StevenNaliwajka/TF2SentryEE/Documentation/1-TurretGuts/PCB/Turret/TurretMainBoard/TurretMainBoard.kicad_sch

## KiCad design Documentation/1-TurretGuts/PCB/Turret/TurretMainBoard/TurretMainBoard.kicad_sch (2025-07-17)

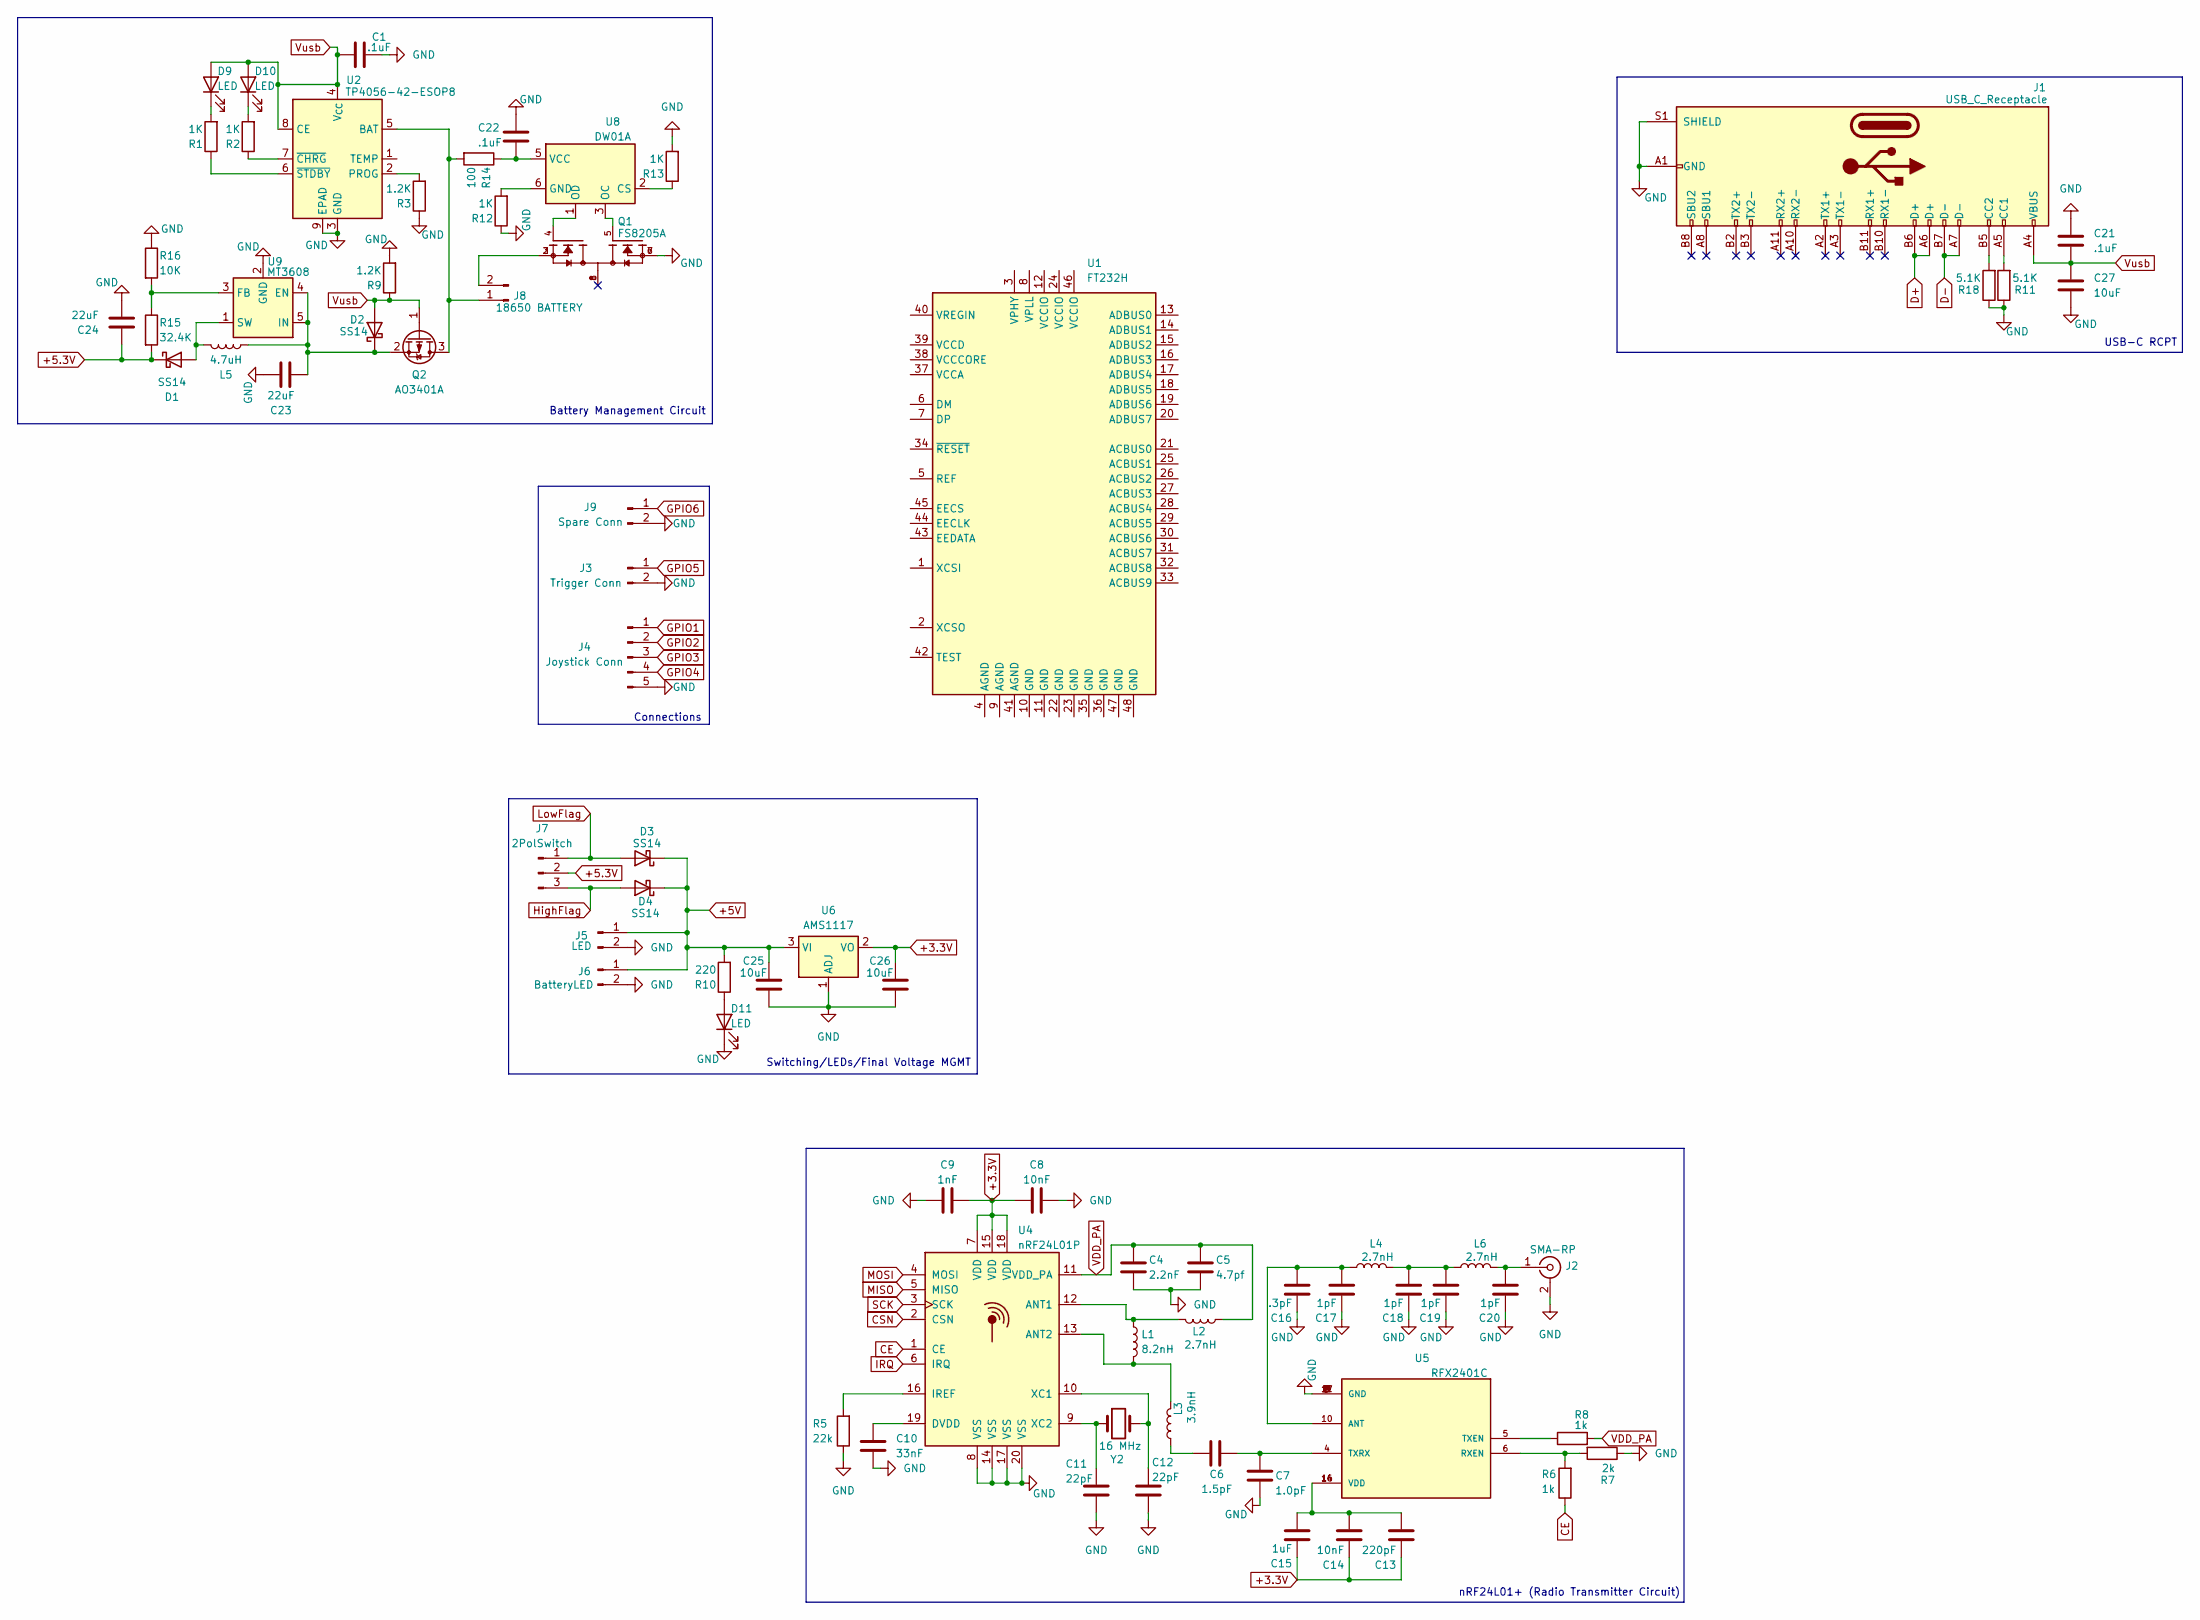
[picture p3: schematic TurretMainBoard.kicad_sch]

Parts:
C1, C21, C22: .1uF
C4: 2.2nF
C5: 4.7pf
C6: 1.5pF
C7: 1.0pF
C8, C14: 10nF
C9: 1nF
C10: 33nF
C11, C12: 22pF
C13: 220pF
C15: 1uF
C16: .3pF
C17, C18, C19, C20: 1pF
C23, C24: 22uF
C25, C26, C27: 10uF
D1, D2, D3, D4: SS14; D_SMA
D9, D10, D11: LED
J1: USB_C_Receptacle
J2: SMA-RP
J3: Trigger Conn
J4: Joystick Conn
J5: LED
J6: BatteryLED
J7: 2PolSwitch
J8: 18650 BATTERY
J9: Spare Conn
L1: 8.2nH
L2, L4, L6: 2.7nH
L3: 3.9nH
L5: 4.7uH
Q1: FS8205A; SOP65P640X120-8N; PARTREV 1.7
Q2: AO3401A; SOT-23
R1, R2, R12, R13: 1K
R3, R9: 1.2K
R5: 22k
R6, R8: 1k
R7: 2k
R10: 220
R11, R18: 5.1K
R14: 100
R15: 32.4K
R16: 10K
U1: FT232H
U2: TP4056-42-ESOP8; SOIC-8-1EP_3.9x4.9mm_P1.27mm_EP2.41x3.3mm_ThermalVias
U4: nRF24L01P; QFN-20-1EP_4x4mm_P0.5mm_EP2.5x2.5mm
U5: RFX2401C; QFN50P300X300X60-17N
U6: AMS1117; SOT-223-3_TabPin2
U8: DW01A; SOT-23-6
U9: MT3608; SOT-23-6
Y2: 16 MHz

Connections:
+3.3V: C8.1, C9.2, C13.2, C14.2, C15.2, C26.1, U4.7 (VDD), U4.15 (VDD), U4.18 (VDD), U6.2 (VO)
+5.3V: C24.2, D1.1 (K), J7.2, R15.2
+5V: C25.1, D3.1 (K), D4.1 (K), J5.1, J6.1, R10.2, U6.3 (VI)
CE: R6.1, U4.1 (CE)
CSN: U4.2 (CSN)
D+: J1.A6 (D+), J1.B6 (D+)
D-: J1.A7 (D-), J1.B7 (D-)
GND: C1.2, C4.2, C5.2, C7.1, C8.2, C9.1, C10.2, C11.2, C12.2, C16.2, C17.2, C18.2, C19.2, C20.2, C21.1, C22.1, C23.2, C24.1, C25.2, C26.2, C27.2, D11.1 (K), J1.A1 (GND), J1.A12 (GND), J1.B1 (GND), J1.B12 (GND), J1.S1 (SHIELD), J2.2 (Ext), J3.2, J4.5, J5.2, J6.2, J9.2, Q1.6, Q1.7, R3.1, R5.1, R7.1, R9.2, R11.1, R12.1, R13.2, R16.1, R18.1, U2.3 (GND), U2.9 (EPAD), U4.8 (VSS), U4.14 (VSS), U4.17 (VSS), U4.20 (VSS), U5.2 (GND), U5.3 (GND), U5.8 (GND), U5.9 (GND), U5.11 (GND), U5.17 (GND), U6.1 (ADJ), U9.2 (GND)
GPIO1: J4.1
GPIO2: J4.2
GPIO3: J4.3
GPIO4: J4.4
GPIO5: J3.1
GPIO6: J9.1
HighFlag: D4.2 (A), J7.3
IRQ: U4.6 (IRQ)
LowFlag: D3.2 (A), J7.1
MISO: U4.5 (MISO)
MOSI: U4.4 (MOSI)
unnamed: C6.1, L3.1
unnamed: C6.2, C7.2, U5.4 (TXRX)
unnamed: C10.1, U4.19 (DVDD)
unnamed: C11.1, U4.9 (XC2), Y2.1
unnamed: C12.1, U4.10 (XC1), Y2.2
unnamed: C13.1, C14.1, C15.1, U5.14 (VDD), U5.16 (VDD)
unnamed: C16.1, C17.1, L4.1, U5.10 (ANT)
unnamed: C18.1, C19.1, L4.2, L6.1
unnamed: C20.1, J2.1 (In), L6.2
unnamed: C22.2, R14.1, U8.5 (VCC)
unnamed: C23.1, D2.1 (K), L5.1, Q2.2 (S), U9.4 (EN), U9.5 (IN)
unnamed: D1.2 (A), L5.2, U9.1 (SW)
unnamed: D9.1 (K), R1.2
unnamed: D10.1 (K), R2.2
unnamed: D11.2 (A), R10.1
unnamed: J1.A5 (CC1), R11.2
unnamed: J1.B5 (CC2), R18.2
unnamed: J8.1, Q2.3 (D), R14.2, U2.5 (BAT)
unnamed: J8.2, Q1.2, Q1.3
unnamed: L1.1, L2.2, U4.12 (ANT1)
unnamed: L1.2, L3.2, U4.13 (ANT2)
unnamed: Q1.1, Q1.8
unnamed: Q1.4, U8.1 (OD)
unnamed: Q1.5, U8.3 (OC)
unnamed: R1.1, U2.6 (~STDBY)
unnamed: R2.1, U2.7 (~CHRG)
unnamed: R3.2, U2.2 (PROG)
unnamed: R5.2, U4.16 (IREF)
unnamed: R6.2, R7.2, U5.6 (RXEN)
unnamed: R8.1, U5.5 (TXEN)
unnamed: R12.2, U8.6 (GND)
unnamed: R13.1, U8.2 (CS)
unnamed: R15.1, R16.2, U9.3 (FB)
SCK: U4.3 (SCK)
VDD_PA: C4.1, C5.1, L2.1, R8.2, U4.11 (VDD_PA)
Vusb: C1.1, C21.2, C27.1, D2.2 (A), D9.2 (A), D10.2 (A), J1.A4 (VBUS), J1.A9 (VBUS), J1.B4 (VBUS), J1.B9 (VBUS), Q2.1 (G), R9.1, U2.4 (V_{CC}), U2.8 (CE)

Notes on the sheet:
Switching/LEDs/Final Voltage MGMT
Connections
USB-C RCPT
nRF24L01+ (Radio Transmitter Circuit)
Battery Management Circuit
